algarv/Ball_Balancing_Robot/img/calibration.png

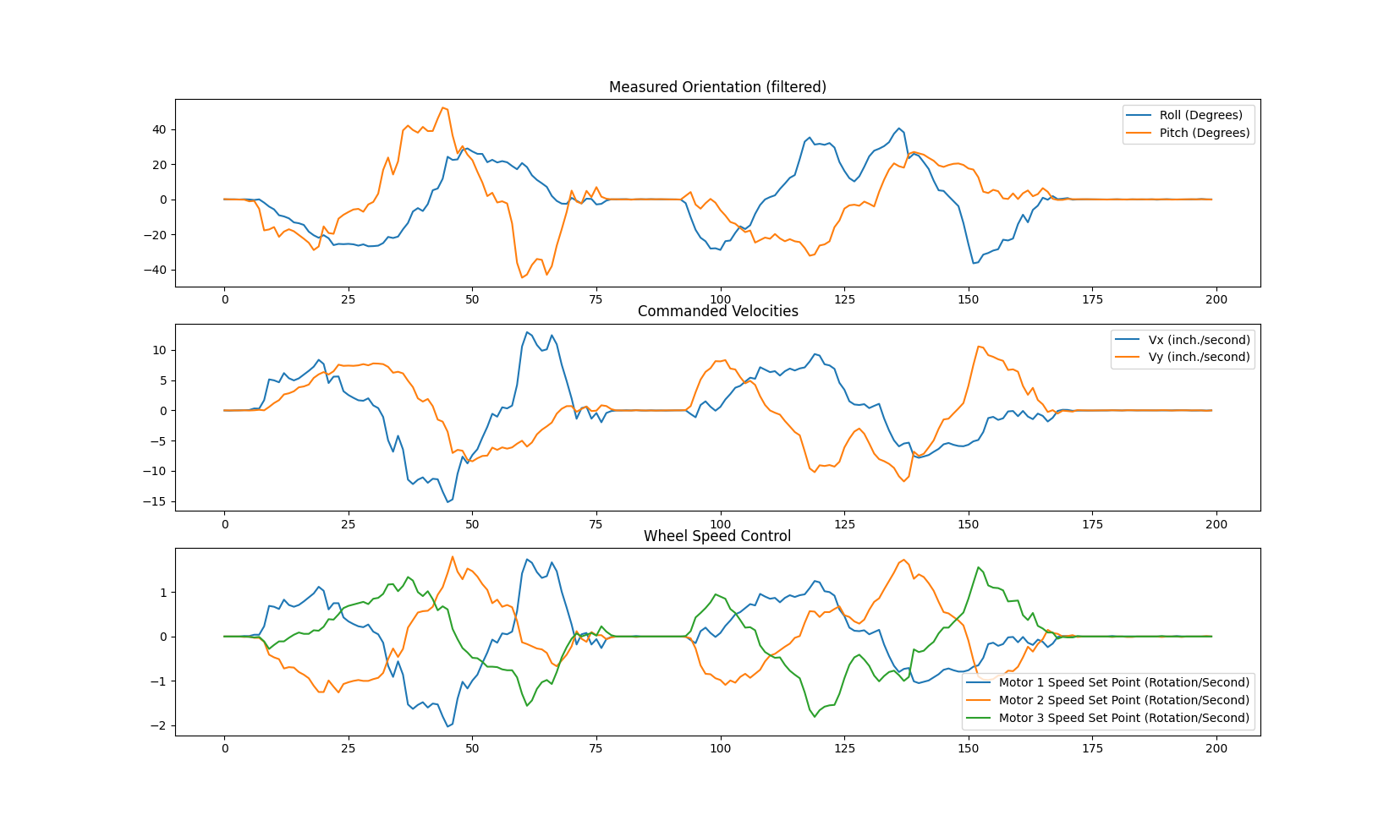
img/calibration.png
